acseka360/sws_lbn/firmware/variants/nrf52840/diy/sws_lbn/variant.cpp

#include "variant.h"
#include "nrf.h"
#include "wiring_constants.h"
#include "wiring_digital.h"

const uint32_t g_ADigitalPinMap[] = {
    /* P0 */
    0, 1, 2, 3, 4, 5, 6, 7,
    8, 9, 10, 11, 12, 13, 14, 15,
    16, 17, 18, 19, 20, 21, 22, 23,
    24, 25, 26, 27, 28, 29, 30, 31,
    /* P1 */
    32, 33, 34, 35, 36, 37, 38, 39,
    40, 41, 42, 43, 44, 45, 46, 47,
};

void initVariant()
{
    NRF_POWER->DCDCEN = 1;
}

void variant_shutdown()
{
    /* No wake source on this PCB — HAS_CPU_SHUTDOWN=0 in variant.h */
}
